OxfordInstrumentsRecruitment/51-G-1128-719/KiCad_Project/PCB_Graphics/ESD/ESD_Silk_8mm.bmp

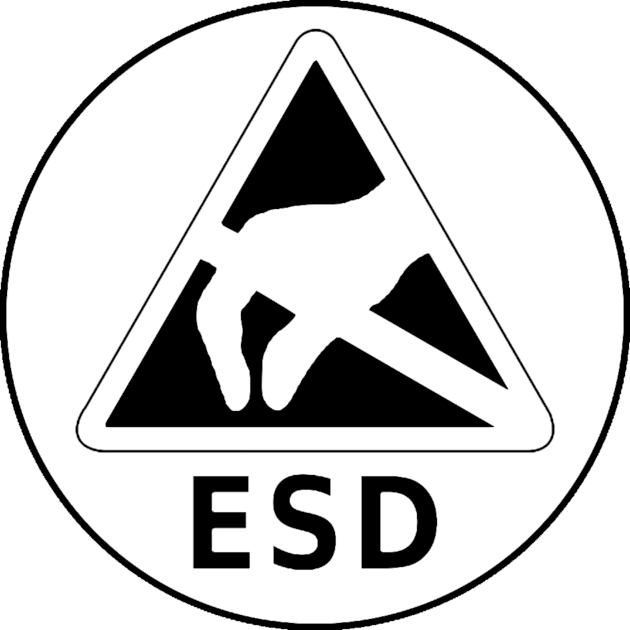
KiCad_Project/PCB_Graphics/ESD/ESD_Silk_8mm.bmp
