OxfordInstrumentsRecruitment/51-G-1128-719/KiCad_Project/PCB_Graphics/Github_Link/github_link.bmp

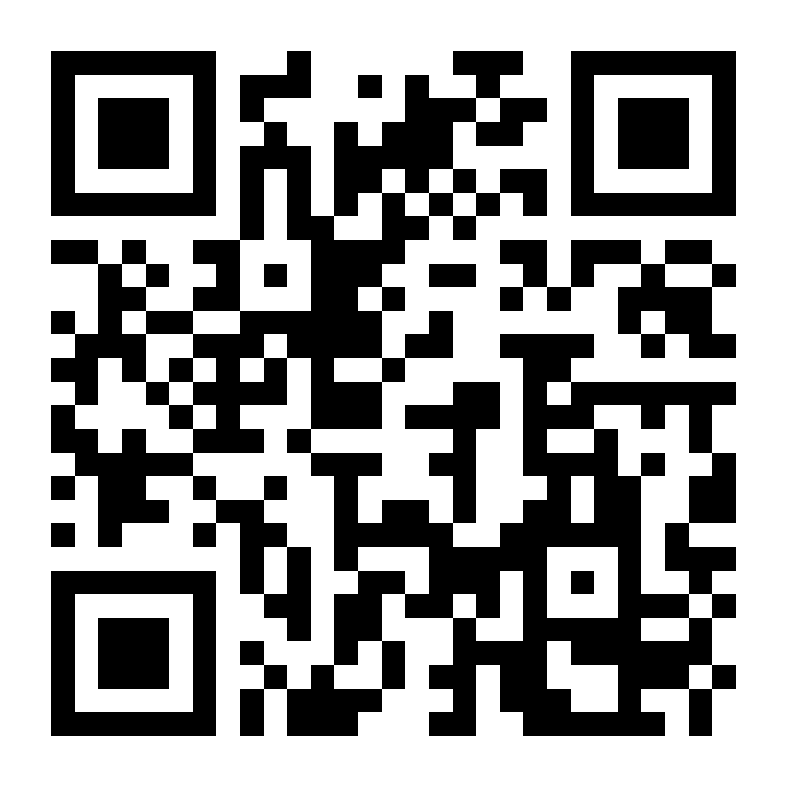
KiCad_Project/PCB_Graphics/Github_Link/github_link.bmp
