OxfordInstrumentsRecruitment/51-G-1128-719/KiCad_Project/PCB_Graphics/OI_Careers_Link/OI_Careers_link.BMP

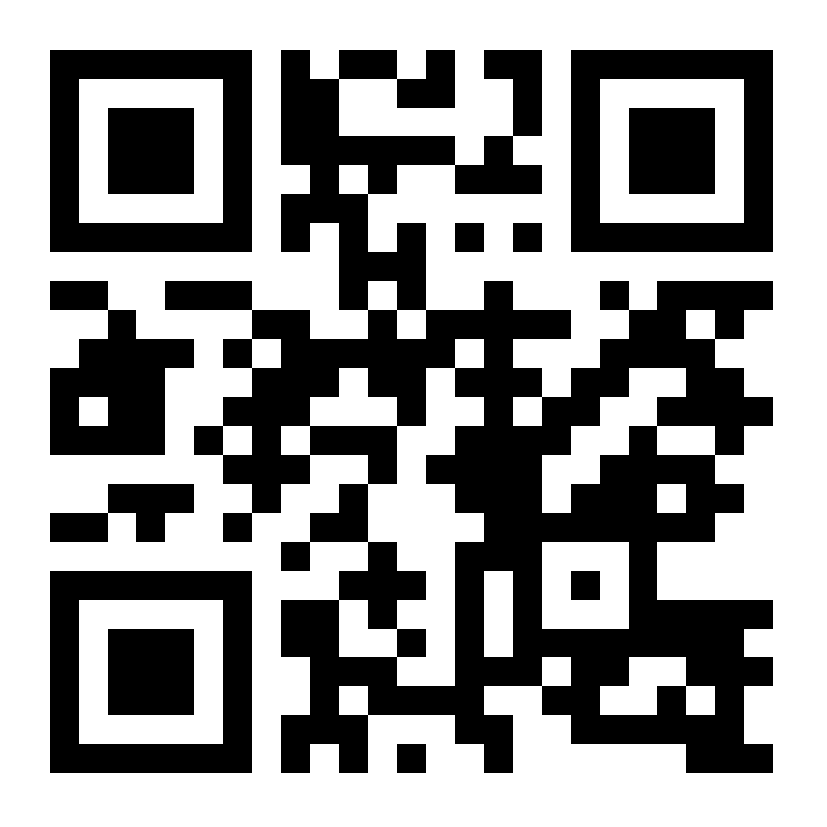
KiCad_Project/PCB_Graphics/OI_Careers_Link/OI_Careers_link.BMP
