OxfordInstrumentsRecruitment/51-G-1128-719/KiCad_Project/PCB_Graphics/PB_Free/PB_FREE.png

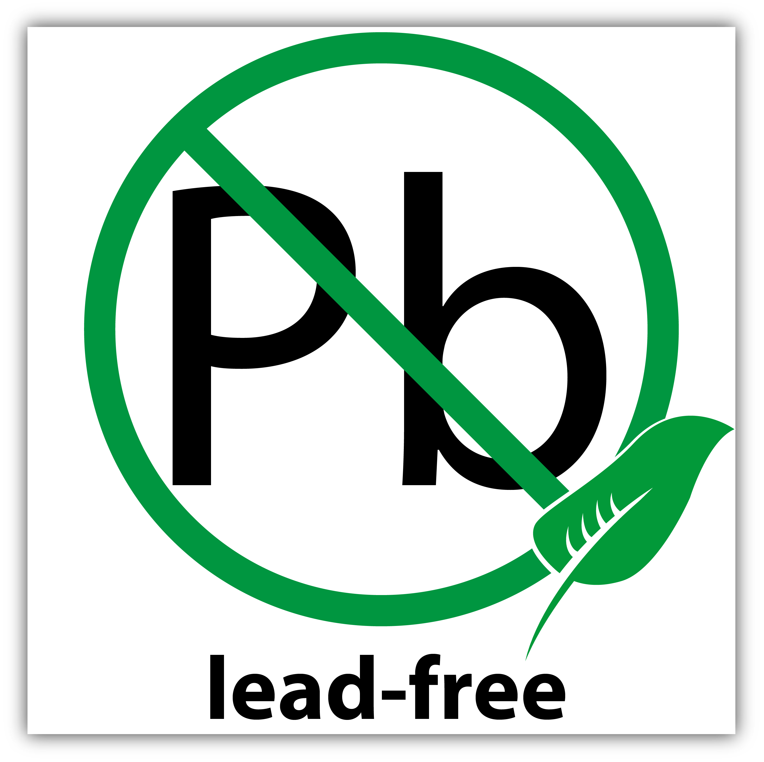
KiCad_Project/PCB_Graphics/PB_Free/PB_FREE.png
