OxfordInstrumentsRecruitment/51-G-1128-719/Renders/Back_No_components.jpg

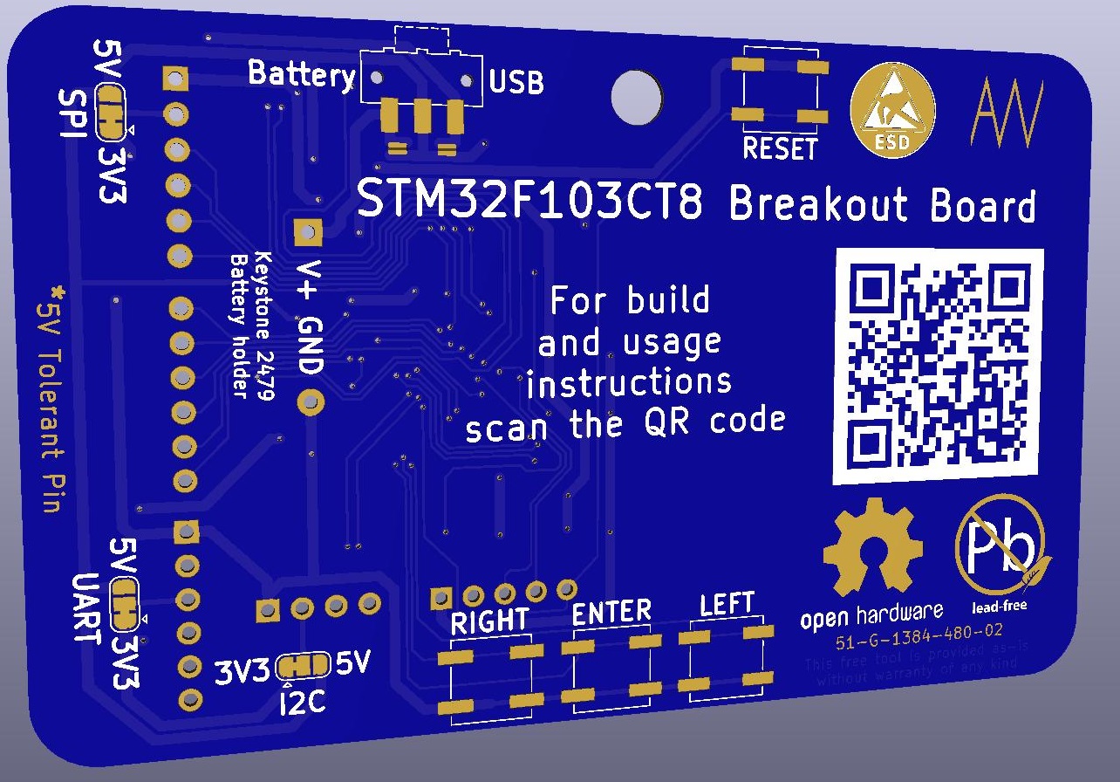
Renders/Back_No_components.jpg
