OxfordInstrumentsRecruitment/51-G-1128-719/Renders/Front_No_components.jpg

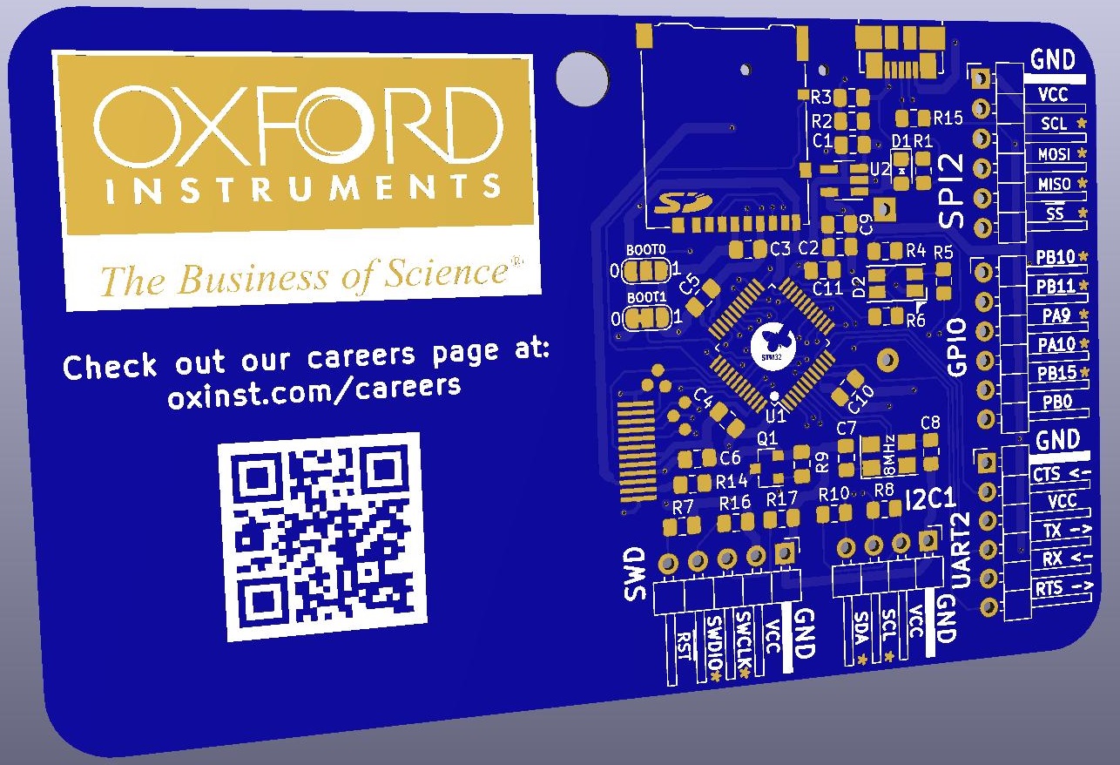
Renders/Front_No_components.jpg
