OxfordInstrumentsRecruitment/51-G-1128-719/Firmware/Test/SD_Card/2.bmp

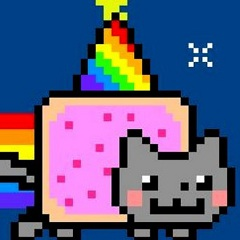
Firmware/Test/SD_Card/2.bmp
