OxfordInstrumentsRecruitment/51-G-1128-719/Simulations/LED_Driver/LED_Driver.asc

D1: LED; LXHL-BW02
Q1: npn; DI_MMBT4401
Q2: npn; DI_MMBT4401
R1: res; 1500
R2: res; 10
V1: voltage; PWL(0 7 0.05 7 0.2 0)
V2: voltage; PULSE(0 3.3 0 1n 1n 10u 20u)
Named nets: 0
.tran 0.2
.include E:\\Personal\\Latimer\\Star_Lights\\Simulations\\Current_Sink\\MMBT4401.txt
